funky-monkey/hijack-main/iPhone/EKGmon/core-plot/systemtests/tests/TestResources/CPGradientTests-testDrawSwatchRendersCorrectlyForFactoryGradients-aquaSelectedGradient.tiff

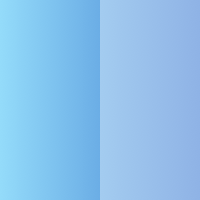
iPhone/EKGmon/core-plot/systemtests/tests/TestResources/CPGradientTests-testDrawSwatchRendersCorrectlyForFactoryGradients-aquaSelectedGradient.tiff
