funky-monkey/hijack-main/iPhone/EKGmon/core-plot/documentation/Classes.graffle/image1.png

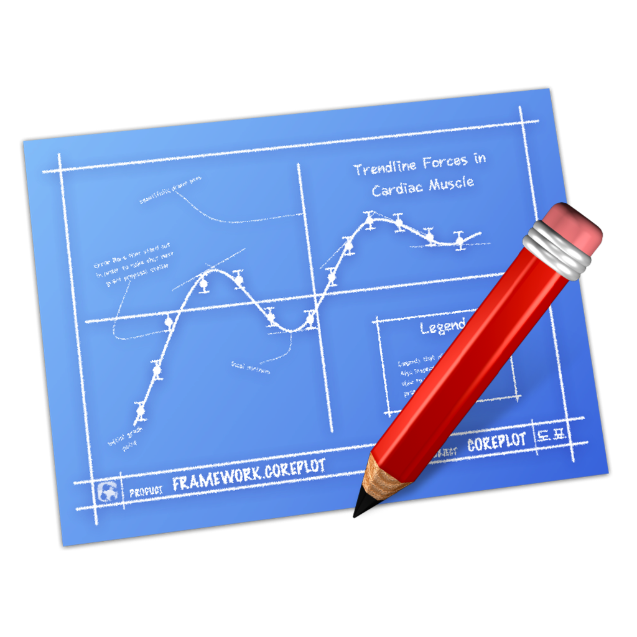
iPhone/EKGmon/core-plot/documentation/Classes.graffle/image1.png
