funky-monkey/hijack-main/iPhone/EKGmon/core-plot/examples/CorePlotGallery/img/PlotGallery128.png

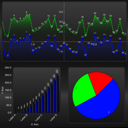
iPhone/EKGmon/core-plot/examples/CorePlotGallery/img/PlotGallery128.png
