funky-monkey/hijack-main/iPhone/EKGmon/core-plot/examples/CPTestApp/Resources/BlueTexture.png

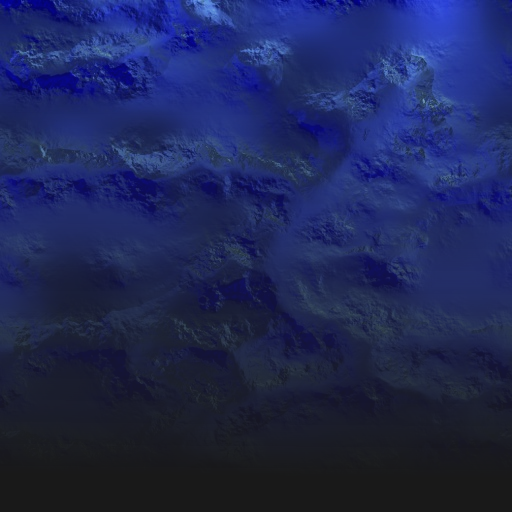
iPhone/EKGmon/core-plot/examples/CPTestApp/Resources/BlueTexture.png
