funky-monkey/hijack-main/iPhone/oscilloscope/Resources/images/oscilloscope.png

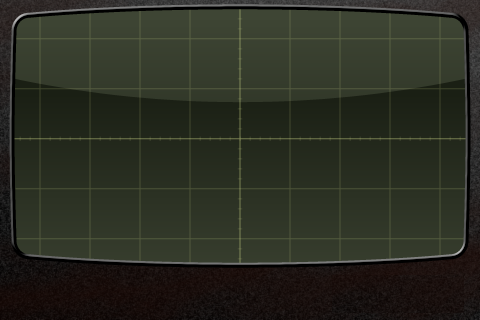
iPhone/oscilloscope/Resources/images/oscilloscope.png
