funky-monkey/hijack-main/iPhone/EKGmon/core-plot/systemtests/google-toolbox-for-mac/AppKit/TestData/GTMNSBezierPath+RoundRectTest.ppc64.tiff

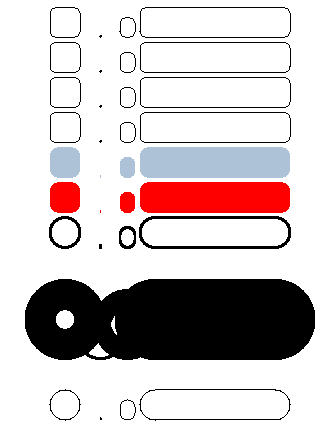
iPhone/EKGmon/core-plot/systemtests/google-toolbox-for-mac/AppKit/TestData/GTMNSBezierPath+RoundRectTest.ppc64.tiff
