funky-monkey/hijack-main/iPhone/EKGmon/core-plot/systemtests/google-toolbox-for-mac/AppKit/TestData/GTMNSBezierPath+ShadingTest.10.5.tiff

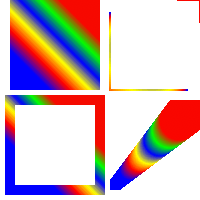
iPhone/EKGmon/core-plot/systemtests/google-toolbox-for-mac/AppKit/TestData/GTMNSBezierPath+ShadingTest.10.5.tiff
