funky-monkey/hijack-main/iPhone/EKGmon/core-plot/systemtests/google-toolbox-for-mac/UnitTesting/GTMUIViewUnitTestingTest.png

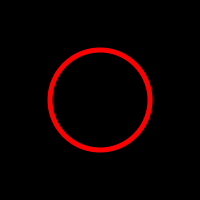
iPhone/EKGmon/core-plot/systemtests/google-toolbox-for-mac/UnitTesting/GTMUIViewUnitTestingTest.png
