funky-monkey/hijack-main/iPhone/EKGmon/core-plot/systemtests/google-toolbox-for-mac/UnitTesting/TestData/GTMUnitTestingImage.10.6.0.tiff

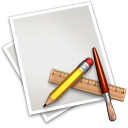
iPhone/EKGmon/core-plot/systemtests/google-toolbox-for-mac/UnitTesting/TestData/GTMUnitTestingImage.10.6.0.tiff
