funky-monkey/hijack-main/iPhone/EKGmon/core-plot/systemtests/google-toolbox-for-mac/UnitTesting/TestData/GTMUnitTestingWindow.10.5.6.tiff

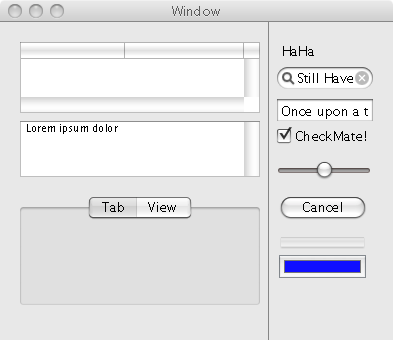
iPhone/EKGmon/core-plot/systemtests/google-toolbox-for-mac/UnitTesting/TestData/GTMUnitTestingWindow.10.5.6.tiff
