funky-monkey/hijack-main/iPhone/EKGmon/core-plot/systemtests/tests/TestResources/CPDarkGradientThemeTests-testApplyThemeToAxisSet.tiff

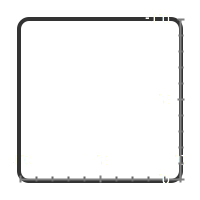
iPhone/EKGmon/core-plot/systemtests/tests/TestResources/CPDarkGradientThemeTests-testApplyThemeToAxisSet.tiff
