funky-monkey/hijack-main/iPhone/EKGmon/core-plot/systemtests/tests/TestResources/CPDarkGradientThemeTests-testApplyThemeToGraph.tiff

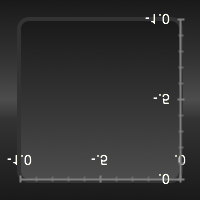
iPhone/EKGmon/core-plot/systemtests/tests/TestResources/CPDarkGradientThemeTests-testApplyThemeToGraph.tiff
