funky-monkey/hijack-main/iPhone/EKGmon/core-plot/systemtests/tests/TestResources/CPDarkGradientThemeTests-testApplyThemeToPlotArea.tiff

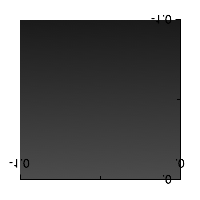
iPhone/EKGmon/core-plot/systemtests/tests/TestResources/CPDarkGradientThemeTests-testApplyThemeToPlotArea.tiff
