funky-monkey/hijack-main/iPhone/EKGmon/core-plot/systemtests/tests/TestResources/CPDarkGradientThemeTests-testRenderGraphWithNoTheme.tiff

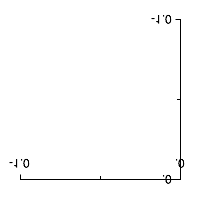
iPhone/EKGmon/core-plot/systemtests/tests/TestResources/CPDarkGradientThemeTests-testRenderGraphWithNoTheme.tiff
