funky-monkey/hijack-main/iPhone/EKGmon/core-plot/systemtests/tests/TestResources/CPGradientTests-testDrawSwatchRendersCorrectlyForFactoryGradients-hydrogenSpectrumGradient.tiff

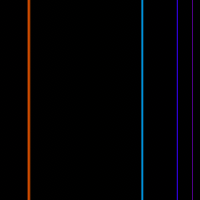
iPhone/EKGmon/core-plot/systemtests/tests/TestResources/CPGradientTests-testDrawSwatchRendersCorrectlyForFactoryGradients-hydrogenSpectrumGradient.tiff
