funky-monkey/hijack-main/iPhone/EKGmon/core-plot/systemtests/tests/TestResources/CPGradientTests-testDrawSwatchRendersCorrectlyForFactoryGradients-rainbowGradient.tiff

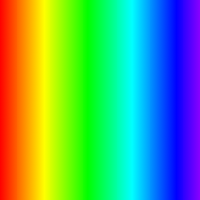
iPhone/EKGmon/core-plot/systemtests/tests/TestResources/CPGradientTests-testDrawSwatchRendersCorrectlyForFactoryGradients-rainbowGradient.tiff
