funky-monkey/hijack-main/iPhone/EKGmon/core-plot/systemtests/tests/TestResources/CPXYGraphTests-testRenderMultipleScatter.tiff

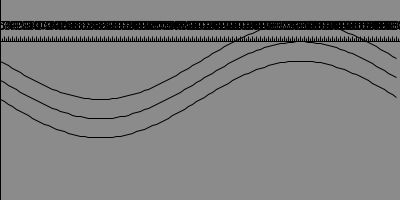
iPhone/EKGmon/core-plot/systemtests/tests/TestResources/CPXYGraphTests-testRenderMultipleScatter.tiff
