funky-monkey/hijack-main/iPhone/EKGmon/core-plot/TestMerge/TestResources/IPhoneOutputGroupTest/Output/CPXYGraphTests-testRenderScatterWithSymbol_Failed_Diff.iPhone.10.6.2.tiff

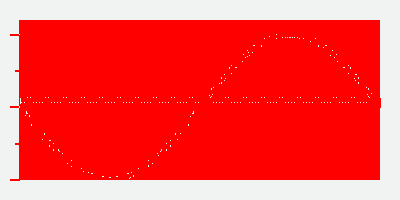
iPhone/EKGmon/core-plot/TestMerge/TestResources/IPhoneOutputGroupTest/Output/CPXYGraphTests-testRenderScatterWithSymbol_Failed_Diff.iPhone.10.6.2.tiff
