funky-monkey/hijack-main/iPhone/EKGmon/core-plot/TestMerge/TestResources/OutputGroupTest/Output/TMMergeControllerTests-testWindowUIRendering2.i386.10.5.7.tiff

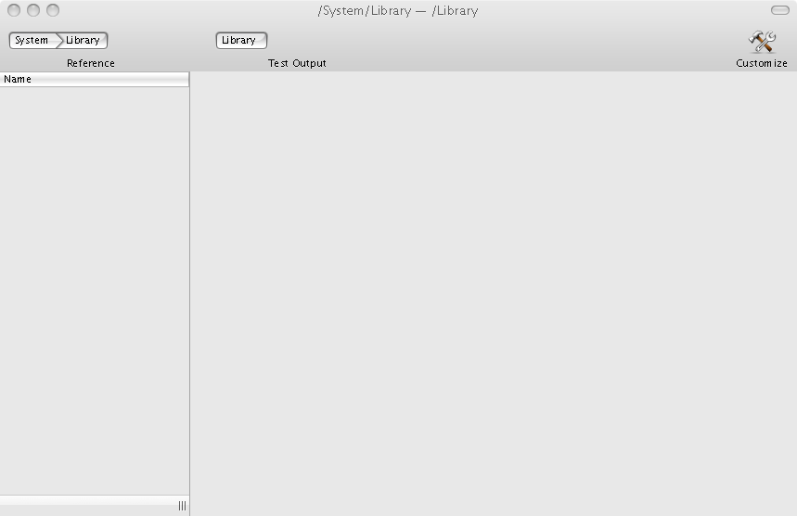
iPhone/EKGmon/core-plot/TestMerge/TestResources/OutputGroupTest/Output/TMMergeControllerTests-testWindowUIRendering2.i386.10.5.7.tiff
