funky-monkey/hijack-main/iPhone/EKGmon/core-plot/TestMerge/TestResources/testmerge-image.tiff

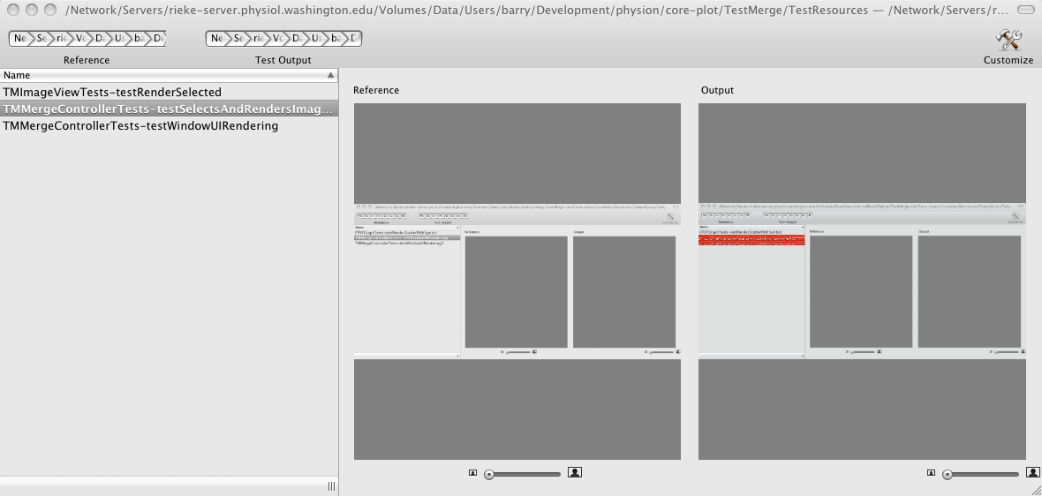
iPhone/EKGmon/core-plot/TestMerge/TestResources/testmerge-image.tiff
