funky-monkey/hijack-main/iPhone/EKGmon/core-plot/TestMerge/TestResources/TMImageViewTests-testOverlayRendering.tiff

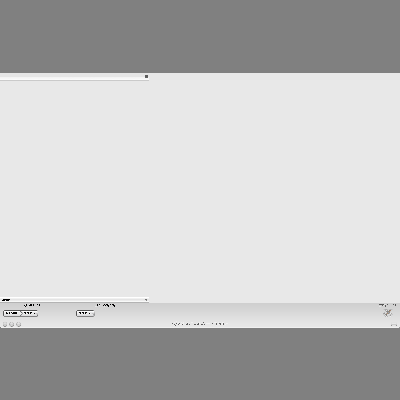
iPhone/EKGmon/core-plot/TestMerge/TestResources/TMImageViewTests-testOverlayRendering.tiff
