funky-monkey/hijack-main/iPhone/EKGmon/core-plot/TestMerge/TestResources/TMMergeControllerTests-testOutputGroupsSortsReferenceAndOutputFiles.tiff

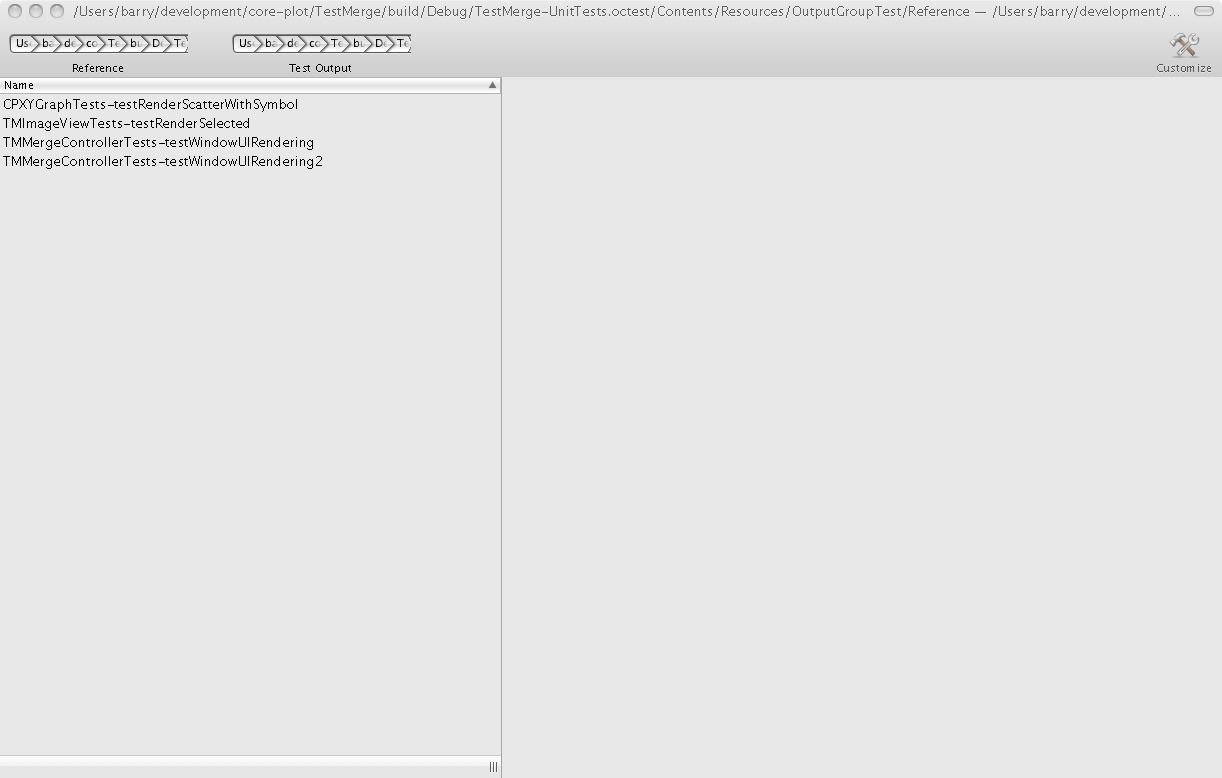
iPhone/EKGmon/core-plot/TestMerge/TestResources/TMMergeControllerTests-testOutputGroupsSortsReferenceAndOutputFiles.tiff
