funky-monkey/hijack-main/iPhone/EKGmon/core-plot/TestMerge/TestResources/TMMergeControllerTests-testSelectsAndRendersImageCompareController+DoNotReplaceReference.tiff

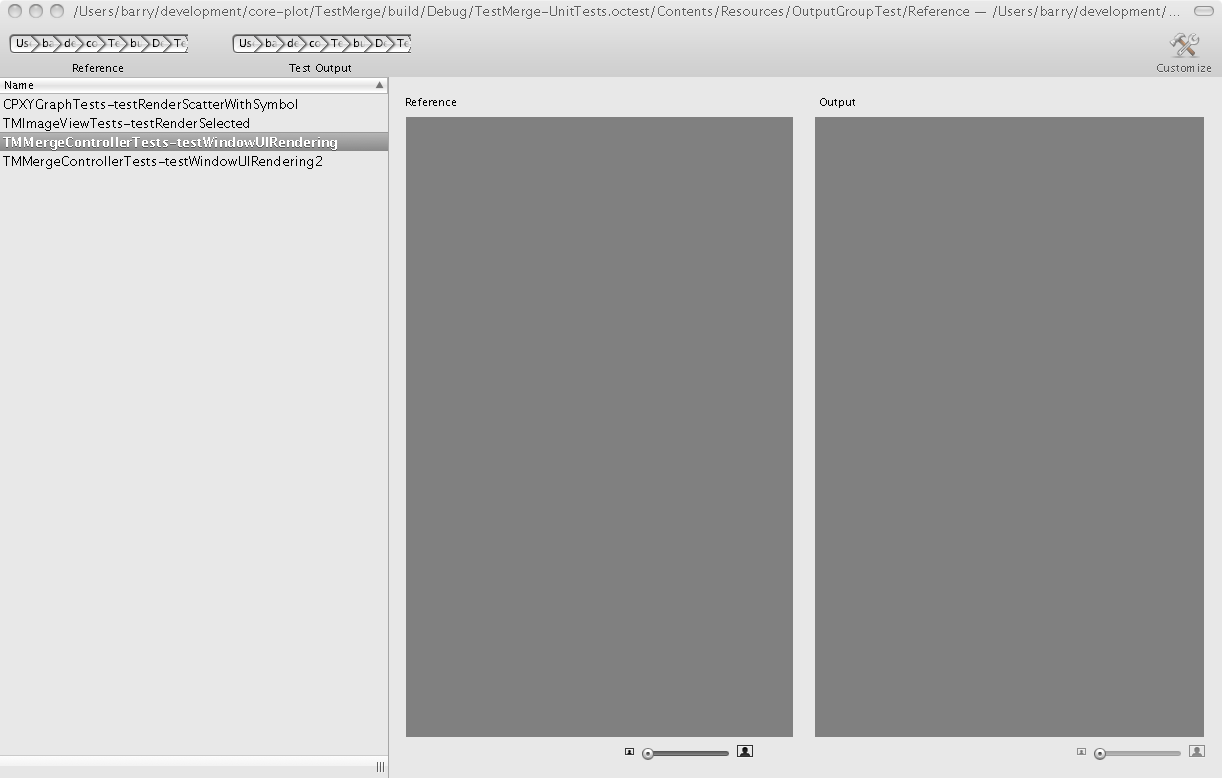
iPhone/EKGmon/core-plot/TestMerge/TestResources/TMMergeControllerTests-testSelectsAndRendersImageCompareController+DoNotReplaceReference.tiff
