funky-monkey/hijack-main/iPhone/EKGmon/core-plot/TestMerge/TestResources/TMMergeControllerTests-testSelectsAndRendersImageCompareController+NilReplaceReference.tiff

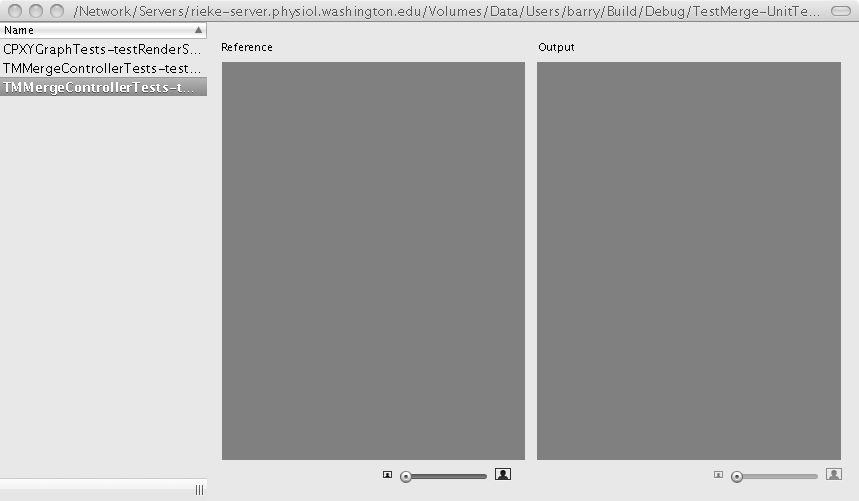
iPhone/EKGmon/core-plot/TestMerge/TestResources/TMMergeControllerTests-testSelectsAndRendersImageCompareController+NilReplaceReference.tiff
