funky-monkey/hijack-main/iPhone/EKGmon/core-plot/TestMerge/TestResources/TMMergeControllerTests-testSelectsAndRendersImageCompareController.tiff

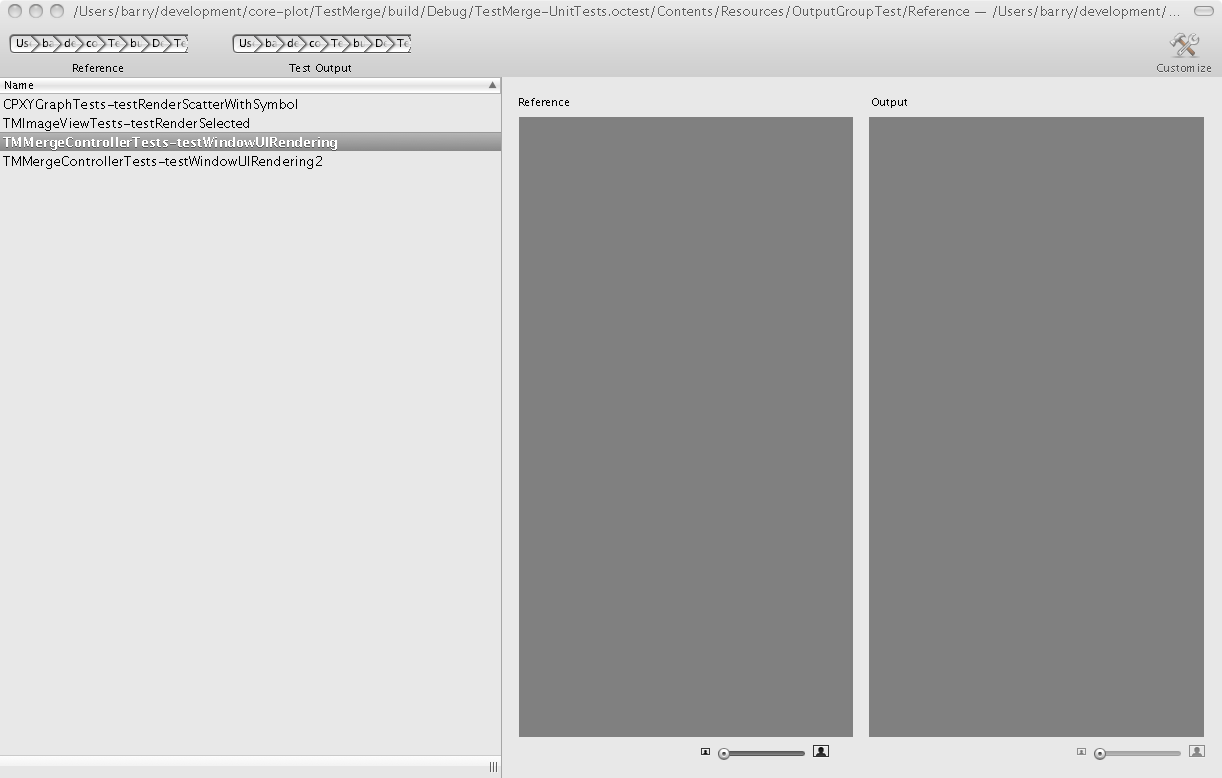
iPhone/EKGmon/core-plot/TestMerge/TestResources/TMMergeControllerTests-testSelectsAndRendersImageCompareController.tiff
