funky-monkey/hijack-main/iPhone/EKGmon/core-plot/TestMerge/TestResources/TMMergeControllerTests-testSelectsAndRendersUTStateCompareController.tiff

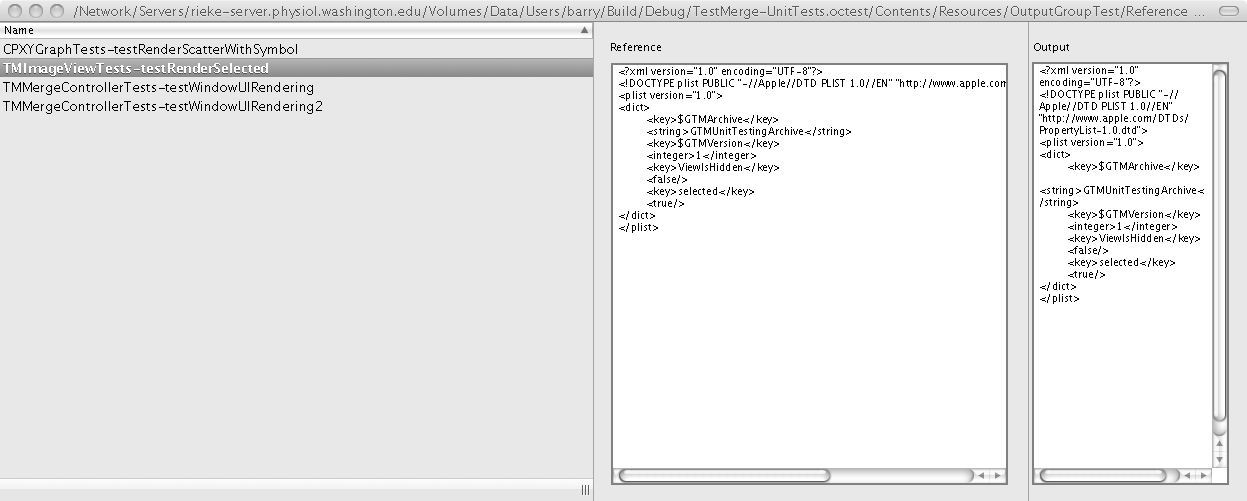
iPhone/EKGmon/core-plot/TestMerge/TestResources/TMMergeControllerTests-testSelectsAndRendersUTStateCompareController.tiff
